veebch/btcticker/images/actionshot/videothumb.png

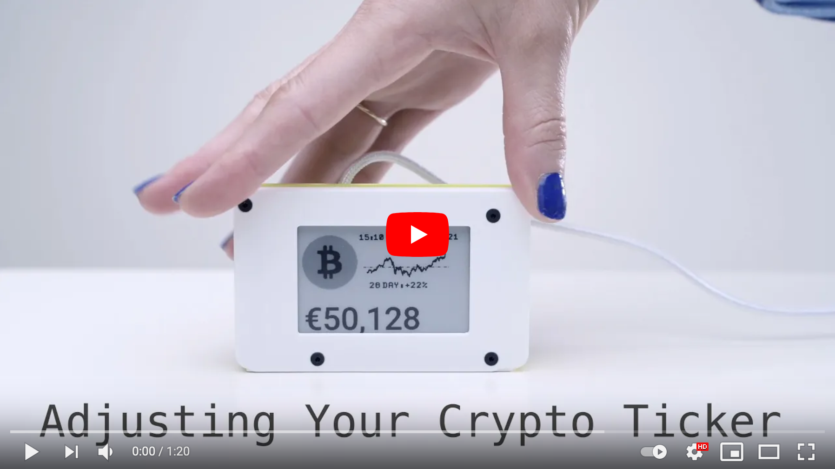
images/actionshot/videothumb.png
